NSLS2/zupsc-hw/daughter/rev2/3dmodels/DFLS130-7_DIO.step

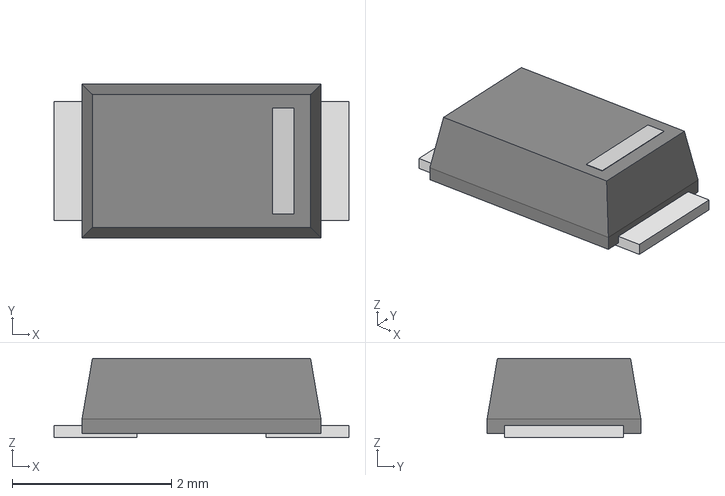
[picture p17: CAD file, 2026-03-28]
daughter/rev2/3dmodels/DFLS130-7_DIO.step
3.70 x 1.93 x 0.997 mm
