NSLS2/zupsc-hw/carrier/revA/3dmodels/IND_LSMG_160808_TAY.step

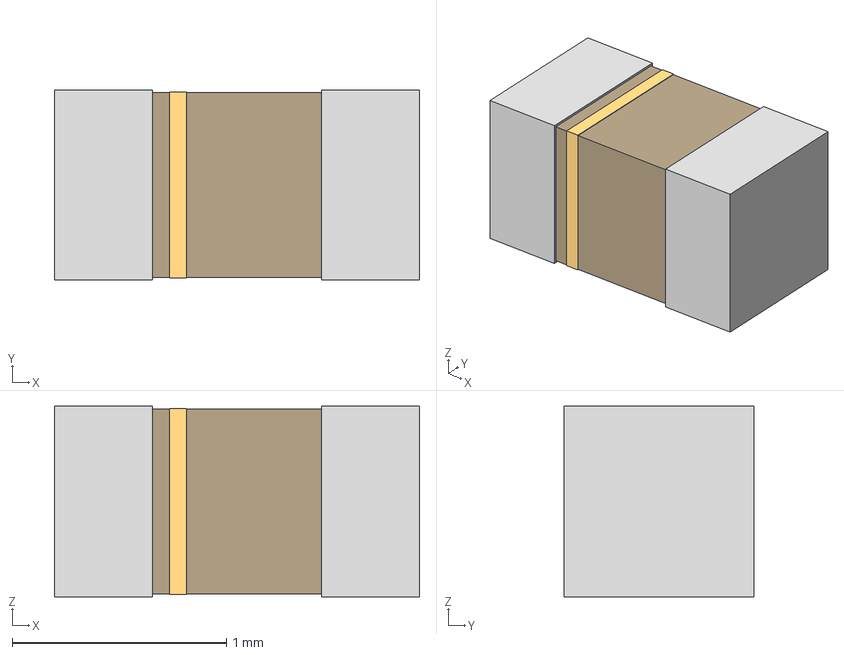
[picture p18: CAD file, 2026-03-28]
carrier/revA/3dmodels/IND_LSMG_160808_TAY.step
1.70 x 0.888 x 0.889 mm
