NSLS2/zupsc-hw/carrier/revA/3dmodels/LTC2991CMS_TRPBF.step

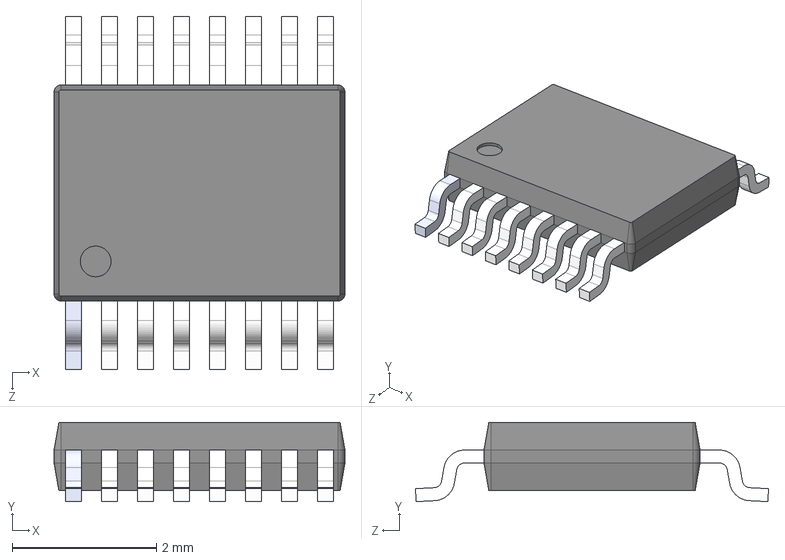
[picture p19: CAD file, 2026-03-28]
carrier/revA/3dmodels/LTC2991CMS_TRPBF.step
4.04 x 1.10 x 4.90 mm
