NSLS2/zupsc-hw/daughter/rev2/3dmodels/RUT0012A.stp

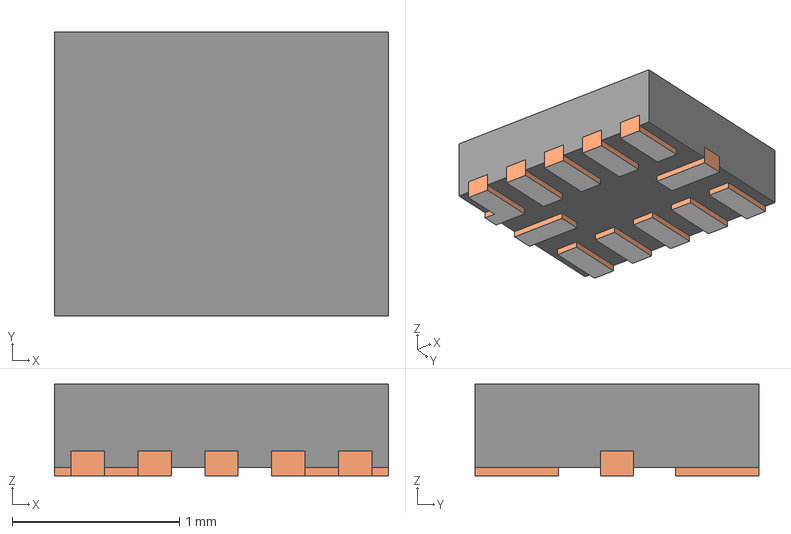
[picture p20: CAD file, 2026-03-28]
daughter/rev2/3dmodels/RUT0012A.stp
2.00 x 1.70 x 0.55 mm
BODY-SON
FRAME-RUT0012A
PIN1-ID
