NSLS2/zupsc-hw/carrier/revA/3dmodels/LT3015EDDPBF.step

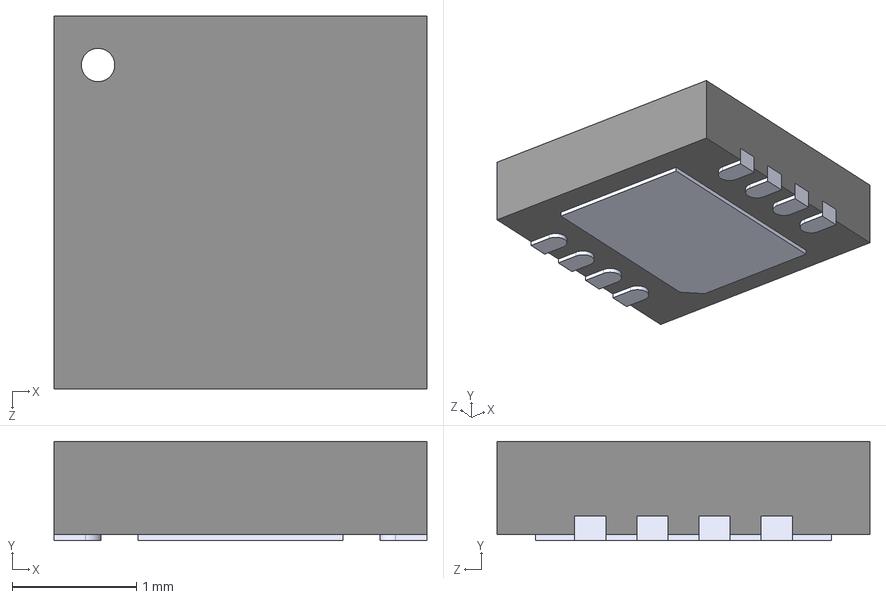
[picture p21: CAD file, 2026-03-28]
carrier/revA/3dmodels/LT3015EDDPBF.step
3.00 x 0.8 x 3.00 mm
