NSLS2/zupsc-hw/daughter/rev2/3dmodels/R_8_ADI.step

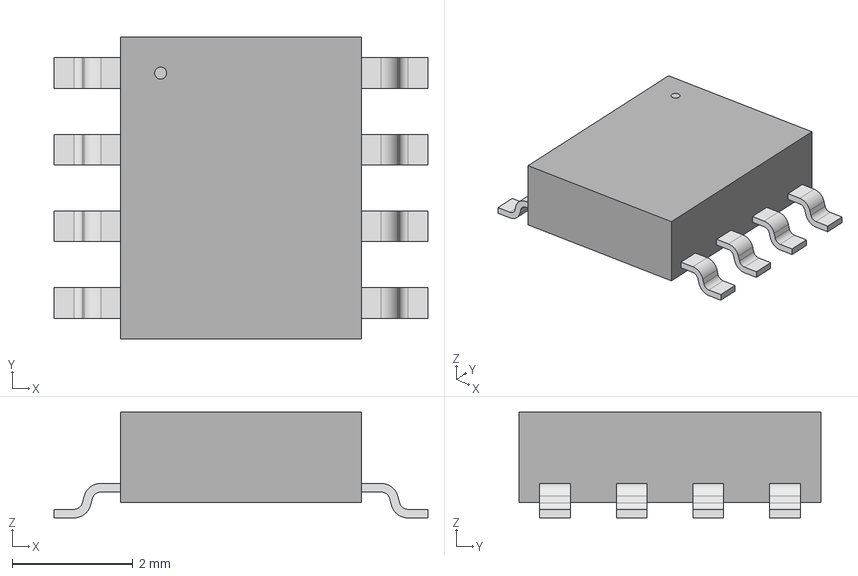
[picture p22: CAD file, 2026-03-28]
daughter/rev2/3dmodels/R_8_ADI.step
6.20 x 5.00 x 1.75 mm
