NSLS2/zupsc-hw/carrier/revA/3dmodels/3-641215-6-z-3d.step

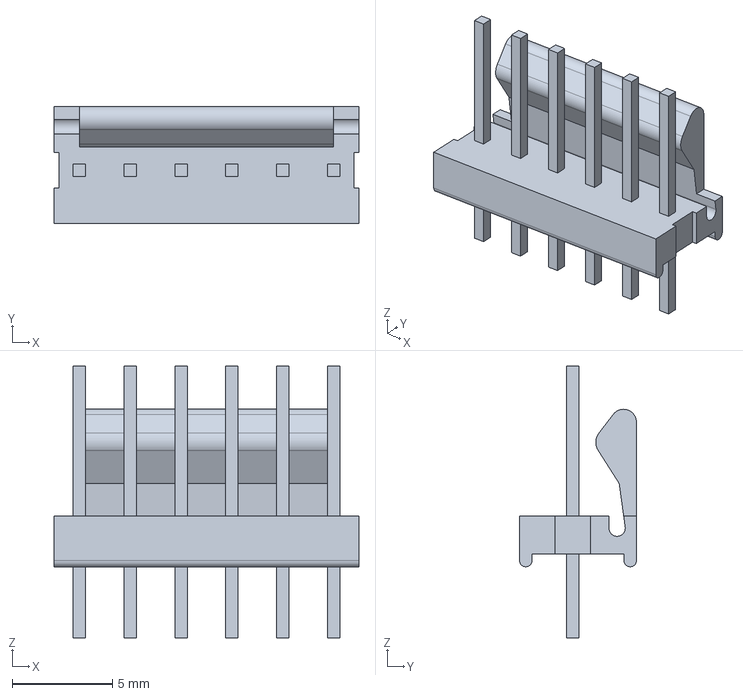
[picture p23: CAD file, 2026-03-28]
carrier/revA/3dmodels/3-641215-6-z-3d.step
15.2 x 5.84 x 13.6 mm
