NSLS2/zupsc-hw/carrier/revA/3dmodels/FUSE_SMDC300F24-2_LTF.step

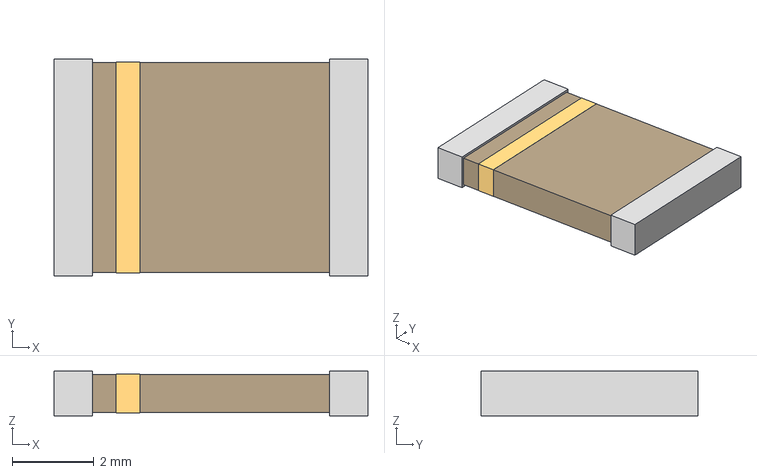
[picture p24: CAD file, 2026-03-28]
carrier/revA/3dmodels/FUSE_SMDC300F24-2_LTF.step
7.70 x 5.31 x 1.09 mm
