NSLS2/zupsc-hw/daughter/rev2/3dmodels/E-20-1_ADI.step

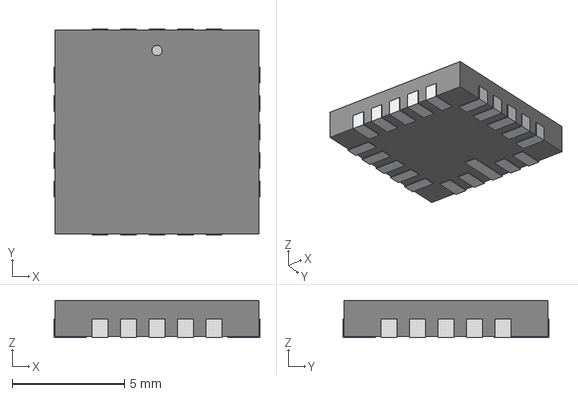
[picture p25: CAD file, 2026-03-28]
daughter/rev2/3dmodels/E-20-1_ADI.step
9.19 x 9.19 x 1.65 mm
