NSLS2/zupsc-hw/daughter/rev2/3dmodels/c-1625854-1-ba-3d.step

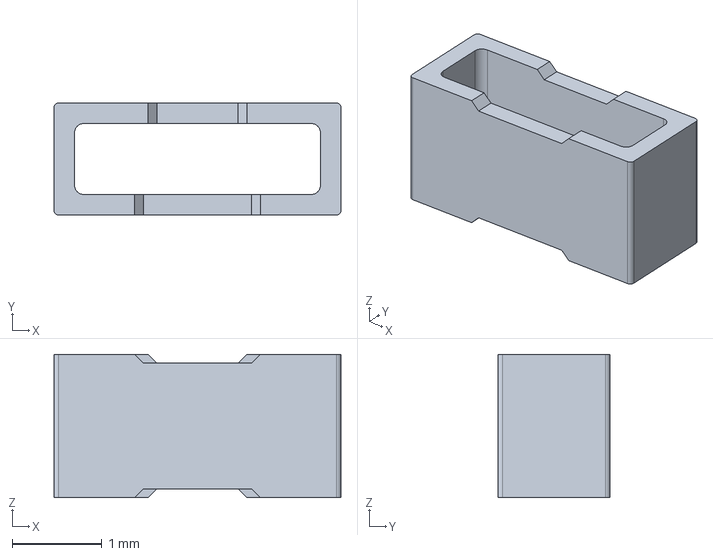
[picture p26: CAD file, 2026-03-28]
daughter/rev2/3dmodels/c-1625854-1-ba-3d.step
3.20 x 1.25 x 1.60 mm
