NSLS2/zupsc-hw/daughter/rev2/3dmodels/ADS8568SPM.step

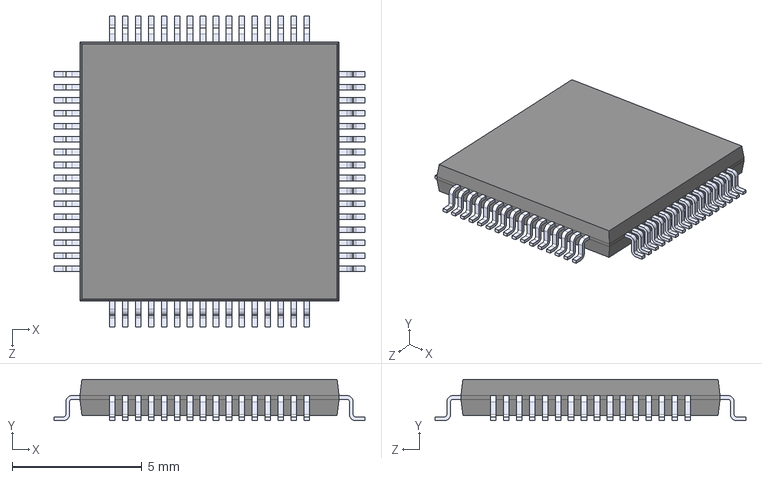
[picture p27: CAD file, 2026-03-28]
daughter/rev2/3dmodels/ADS8568SPM.step
12.0 x 1.60 x 12.0 mm
