NSLS2/zupsc-hw/daughter/rev2/3dmodels/SOT563_LTF.step

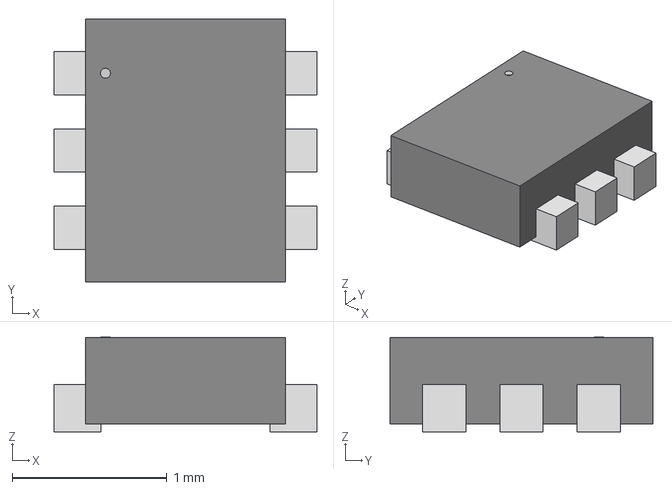
[picture p28: CAD file, 2026-03-28]
daughter/rev2/3dmodels/SOT563_LTF.step
1.70 x 1.70 x 0.612 mm
