NSLS2/zupsc-hw/daughter/rev2/3dmodels/Amphenol_10090926-P264XLF.step

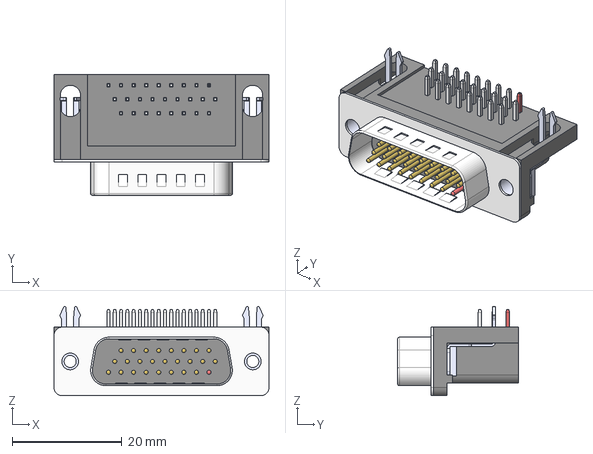
[picture p29: CAD file, 2026-03-28]
daughter/rev2/3dmodels/Amphenol_10090926-P264XLF.step
39.2 x 22.0 x 16.3 mm
