NSLS2/zupsc-hw/daughter/rev2/3dmodels/LTC2378CDE-20#PBF.STEP

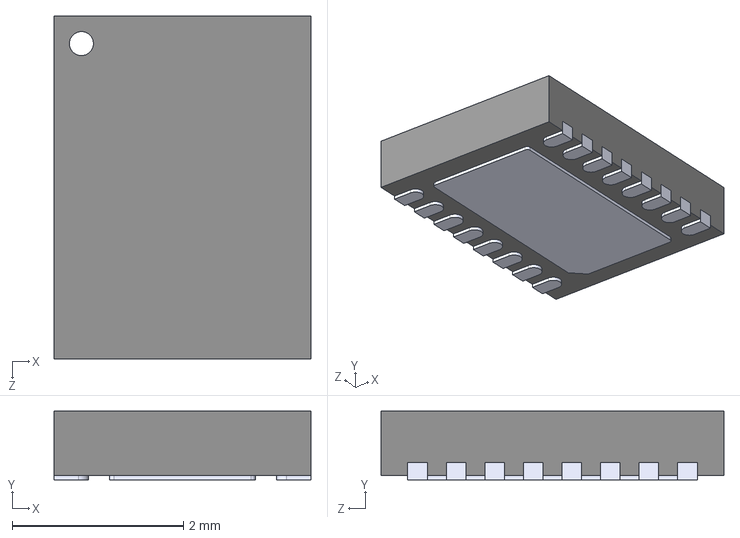
[picture p30: CAD file, 2026-03-28]
daughter/rev2/3dmodels/LTC2378CDE-20#PBF.STEP
3.00 x 0.8 x 4.00 mm
